4n3m4i1/PG_Logic/Boards/ProgrammaGull_Sandpiper/Examples/Sandpiper_v1/DDS/DAC.v

module fods_mod
#(
    parameter DATA_W = 16
)
(
    input mod_clk,
    input [(DATA_W - 1):0]mod_din,
    output wire mod_dout
);

    reg [(DATA_W):0]mod_accum;
    //reg [(DATA_W - 1):0]mod_buffer;

    assign mod_dout = mod_accum[DATA_W];

    initial begin
        mod_accum = {DATA_W + 1{1'b0}};
        //mod_accum = 0;
    end

    always @ (posedge mod_clk) begin
        //mod_accum <= mod_accum[(DATA_W - 1):0] + mod_buffer;
        //mod_buffer <= mod_din;
        mod_accum <= mod_accum[(DATA_W - 1):0] + mod_din;
    end

endmodule
